samp38/varioSmooth/VarioSMooth.X/pic24f16ka101_ports.h

#define ENABLE_RA0_PULLUP() _CN2PUE = 1
#define DISABLE_RA0_PULLUP() _CN2PUE = 0
#define ENABLE_RA1_PULLUP() _CN3PUE = 1
#define DISABLE_RA1_PULLUP() _CN3PUE = 0
#define ENABLE_RA2_PULLUP() _CN30PUE = 1
#define DISABLE_RA2_PULLUP() _CN30PUE = 0
#define ENABLE_RA3_PULLUP() _CN29PUE = 1
#define DISABLE_RA3_PULLUP() _CN29PUE = 0
#define ENABLE_RA4_PULLUP() _CN0PUE = 1
#define DISABLE_RA4_PULLUP() _CN0PUE = 0

#define ENABLE_RA6_PULLUP() _CN8PUE = 1
#define DISABLE_RA6_PULLUP() _CN8PUE = 0

#define ENABLE_RB0_PULLUP() _CN4PUE = 1
#define DISABLE_RB0_PULLUP() _CN4PUE = 0
#define ENABLE_RB1_PULLUP() _CN5PUE = 1
#define DISABLE_RB1_PULLUP() _CN5PUE = 0

#define ENABLE_RB2_PULLUP() _CN6PUE = 1
#define DISABLE_RB2_PULLUP() _CN6PUE = 0

#define ENABLE_RB4_PULLUP() _CN1PUE = 1
#define DISABLE_RB4_PULLUP() _CN1PUE = 0
#define ENABLE_RB7_PULLUP() _CN23PUE = 1
#define DISABLE_RB7_PULLUP() _CN23PUE = 0
#define ENABLE_RB8_PULLUP() _CN22PUE = 1
#define DISABLE_RB8_PULLUP() _CN22PUE = 0
#define ENABLE_RB9_PULLUP() _CN21PUE = 1
#define DISABLE_RB9_PULLUP() _CN21PUE = 0

#define ENABLE_RB12_PULLUP() _CN14PUE = 1
#define DISABLE_RB12_PULLUP() _CN14PUE = 0
#define ENABLE_RB13_PULLUP() _CN13PUE = 1
#define DISABLE_RB13_PULLUP() _CN13PUE = 0

#define ENABLE_RB14_PULLUP() _CN12PUE = 1
#define DISABLE_RB14_PULLUP() _CN12PUE = 0
#define ENABLE_RB15_PULLUP() _CN11PUE = 1
#define DISABLE_RB15_PULLUP() _CN11PUE = 0

#define ENABLE_RA0_CN_INTERRUPT() _CN2IE = 1
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
}
static inline void CONFIG_RB13_AS_DIG_INPUT(){
 DISABLE_RB13_PULLUP();
 _TRISB13 = 1;
 _PCFG11 = 1;
}
static inline void CONFIG_RB14_AS_DIG_INPUT(){
 DISABLE_RB14_PULLUP();
 _TRISB14 = 1;
 _PCFG10 = 1;
}
static inline void CONFIG_RB15_AS_DIG_INPUT(){
 DISABLE_RB15_PULLUP();
 _TRISB15 = 1;
}


#ifdef _PCFG0
static inline void CONFIG_AN0_AS_ANALOG(){
  CONFIG_RA0_AS_DIG_INPUT();
  _PCFG0 = 0;
}
#endif
#ifdef _PCFG1
static inline void CONFIG_AN1_AS_ANALOG(){
  CONFIG_RA1_AS_DIG_INPUT();
  _PCFG1 = 0;
}
#endif
#ifdef _PCFG2
static inline void CONFIG_AN2_AS_ANALOG(){
  CONFIG_RB0_AS_DIG_INPUT();
  _PCFG2 = 0;
}
#endif
#ifdef _PCFG3
static inline void CONFIG_AN3_AS_ANALOG(){
  CONFIG_RB1_AS_DIG_INPUT();
  _PCFG3 = 0;
}
#endif
#ifdef _PCFG4
static inline void CONFIG_AN4_AS_ANALOG(){
  CONFIG_RA2_AS_DIG_INPUT();
  _PCFG4 = 0;
}
#endif
#ifdef _PCFG5
static inline void CONFIG_AN5_AS_ANALOG(){
  CONFIG_RA3_AS_DIG_INPUT();
  _PCFG5 = 0;
}
#endif
#ifdef _PCFG10
static inline void CONFIG_AN10_AS_ANALOG(){
  CONFIG_RB14_AS_DIG_INPUT();
  _PCFG10 = 0;
}
#endif
#ifdef _PCFG11
static inline void CONFIG_AN11_AS_ANALOG(){
  CONFIG_RB13_AS_DIG_INPUT();
  _PCFG11 = 0;
}
#endif

#define _PIC24_DIGIO_DEFINED
