samp38/varioSmooth/VarioSMooth.X/audio_response.h

/* 
 * File:   audio_response.h
 * Author: sam
 *
 * Created on 22 février 2013, 13:31
 */

#define SPEED_STEP 9
#define SPEED_INDEX_MAX 100-1

#ifndef AUDIO_RESPONSE_H

const u16 beepLen[] =
{
2160,
2150,
2140,
2130,
2100,
2070,
1960,
1867,
1787,
1717,
1657,
1603,
1556,
1513,
1475,
1439,
1407,
1377,
1348,
1322,
1296,
1272,
1249,
1227,
1206,
1185,
1165,
1145,
1126,
1107,
1089,
1071,
1054,
1037,
1020,
1003,
987,
971,
956,
940,
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
}
;

const u16 audioFreq[] =
{
350,
360,
370,
380,
400,
420,
474,
520,
560,
597,
630,
660,
688,
714,
737,
760,
781,
801,
819,
838,
854,
870,
886,
900,
914,
928,
941,
954,
966,
977,
989,
1000,
1011,
1021,
1031,
1041,
1050,
1059,
1069,
1078,
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
};

#endif	/* AUDIO_RESPONSE_H */
