samp38/varioSmooth/VarioSMooth.X/pic24_all.h

/*
 * "Copyright (c) 2008 Robert B. Reese, Bryan A. Jones, J. W. Bruce ("AUTHORS")"
 * All rights reserved.
 * (R. Reese, reese_AT_ece.msstate.edu, Mississippi State University)
 * (B. A. Jones, bjones_AT_ece.msstate.edu, Mississippi State University)
 * (J. W. Bruce, jwbruce_AT_ece.msstate.edu, Mississippi State University)
 *
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
 * IN NO EVENT SHALL THE "AUTHORS" BE LIABLE TO ANY PARTY FOR
 * DIRECT, INDIRECT, SPECIAL, INCIDENTAL, OR CONSEQUENTIAL DAMAGES ARISING OUT
 * OF THE USE OF THIS SOFTWARE AND ITS DOCUMENTATION, EVEN IF THE "AUTHORS"
 * HAS BEEN ADVISED OF THE POSSIBILITY OF SUCH DAMAGE.
 *
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
 * Please maintain this header in its entirety when copying/modifying
 * these files.
 *
 *
 */


// Documentation for this file. If the \file tag isn't present,
// this file won't be documented.
/** \file
 *  This header file includes the all the pic24_*.h files as detailed
 *  in the \ref index and also includes the necessary
 *  processor-specific include file (via a \#include p24h/fxxxx.h).
 */

#ifndef _PIC24_ALL_H_
#define _PIC24_ALL_H_


#include "p24f16ka101.h"

// added HN

// Fosc = LPFRC (500kHz) / CLKDIV
// CLKDIV = 0 (divide by 1) => Fosc = 500kHz
// FCY = Fosc/2 = 250kHz

#define FCY 250000L

// HN

// Include PIC24 support library headers
#include "pic24_generic.h"
//#include "pic24_clockfreq.h"
//#include "pic24_delay.h"
#include "pic24_ports.h"

#ifndef BUILT_ON_ESOS
//#include "pic24_uart.h"
//#include "pic24_serial.h"
//#include "pic24_util.h"
#endif

//#include "pic24_timer.h"
//#include "pic24_i2c.h"
//#include "pic24_spi.h"
//#include "pic24_adc.h"
//#include "pic24_dma.h"
//#include "pic24_ecan.h"
//#include "pic24_flash.h"
//#include "pic24_comparator.h"

#endif // #ifndef  _PIC24_ALL_H_
